PawelZietek/Hexapod-with-Raspberry-and-Maestro/pics, diagrams, videos/0J9911.600x480.jpg

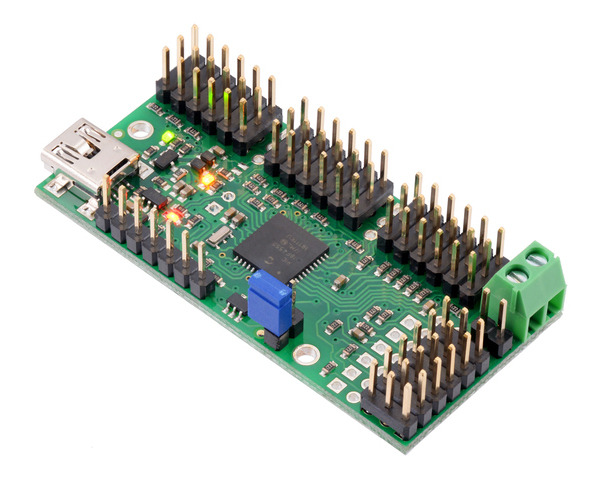
pics, diagrams, videos/0J9911.600x480.jpg
