PawelZietek/Hexapod-with-Raspberry-and-Maestro/pics, diagrams, videos/arm rotating.jpg

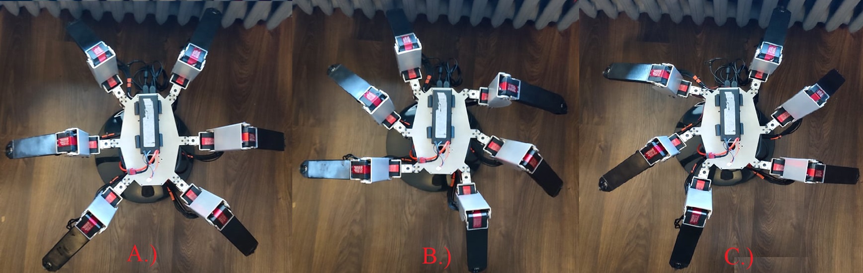
pics, diagrams, videos/arm rotating.jpg
