PawelZietek/Hexapod-with-Raspberry-and-Maestro/pics, diagrams, videos/femurupand down.jpg

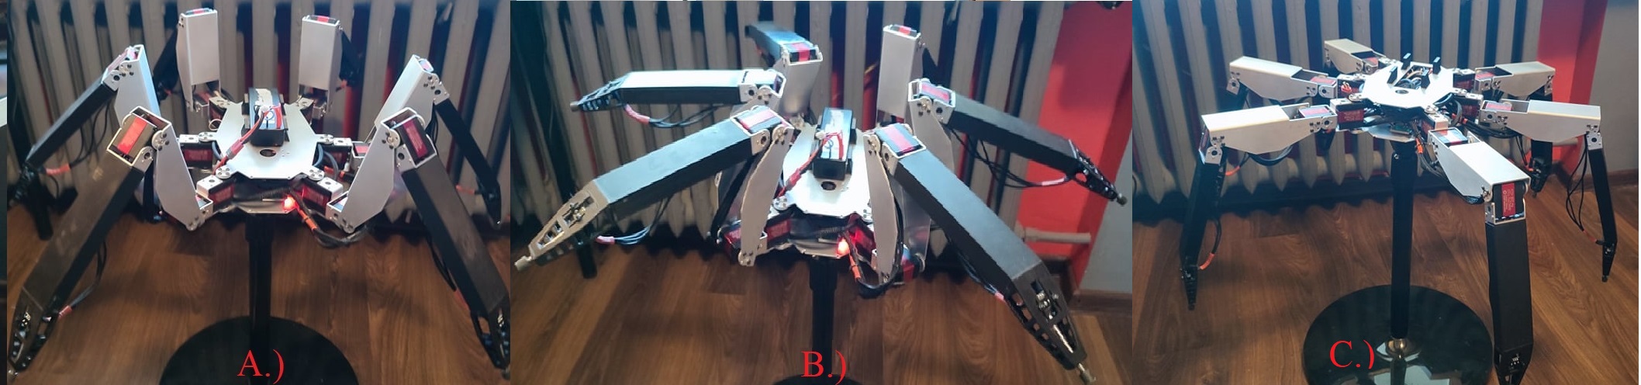
pics, diagrams, videos/femurupand down.jpg
