PawelZietek/Hexapod-with-Raspberry-and-Maestro/pics, diagrams, videos/foot.png

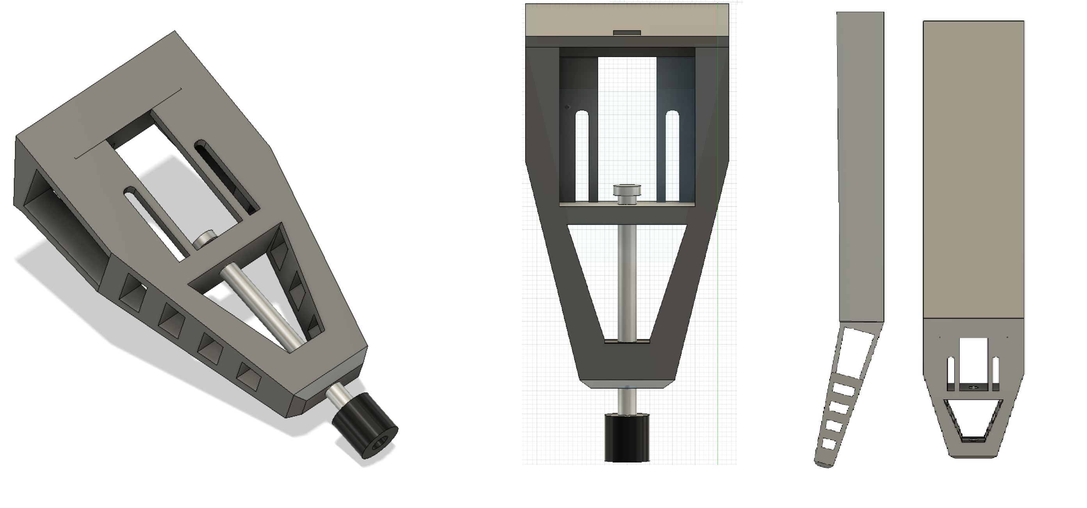
pics, diagrams, videos/foot.png
