PawelZietek/Hexapod-with-Raspberry-and-Maestro/pics, diagrams, videos/forwardbacwardsequence.PNG

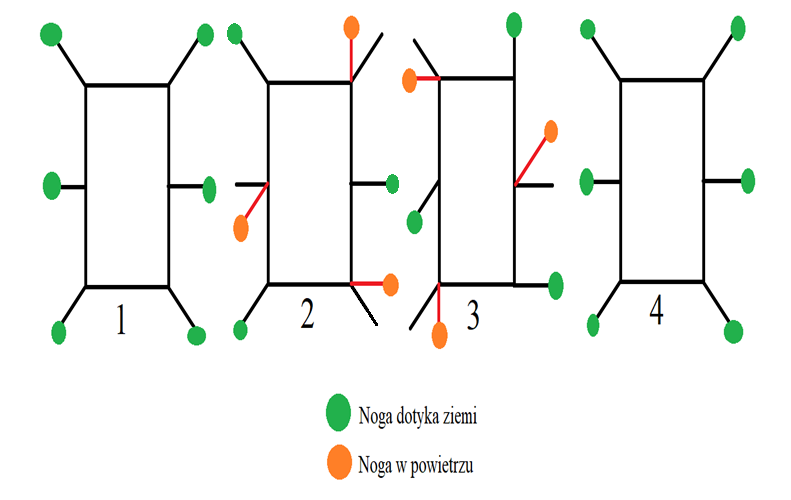
pics, diagrams, videos/forwardbacwardsequence.PNG
