PawelZietek/Hexapod-with-Raspberry-and-Maestro/pics, diagrams, videos/gpio connection.png

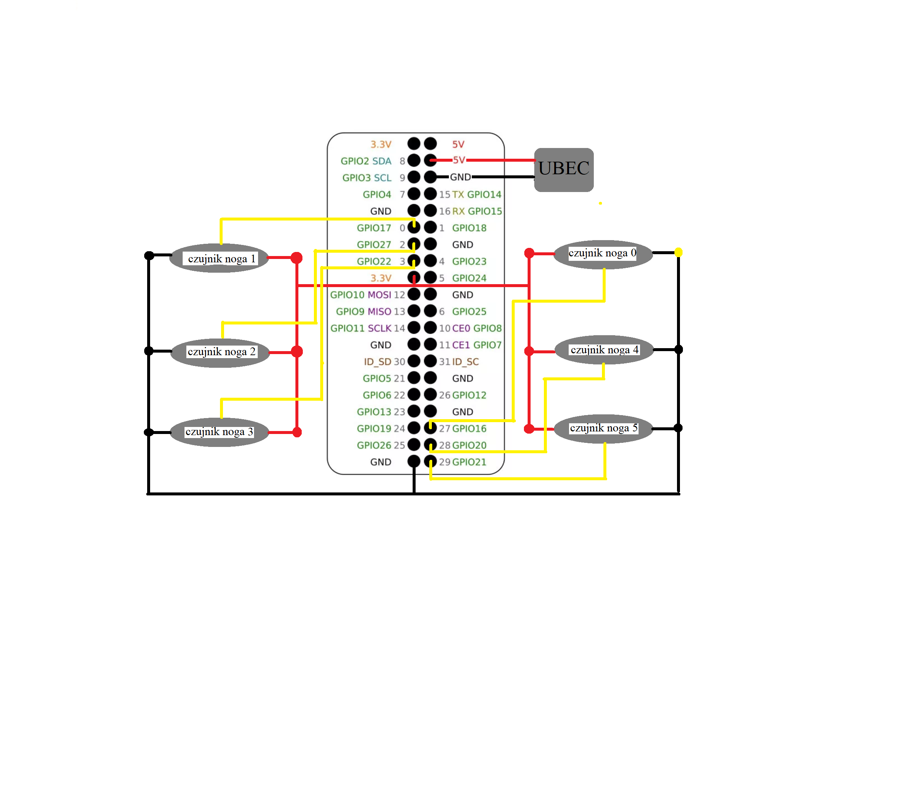
pics, diagrams, videos/gpio connection.png
