PawelZietek/Hexapod-with-Raspberry-and-Maestro/pics, diagrams, videos/hexapod_drawings 1.PNG

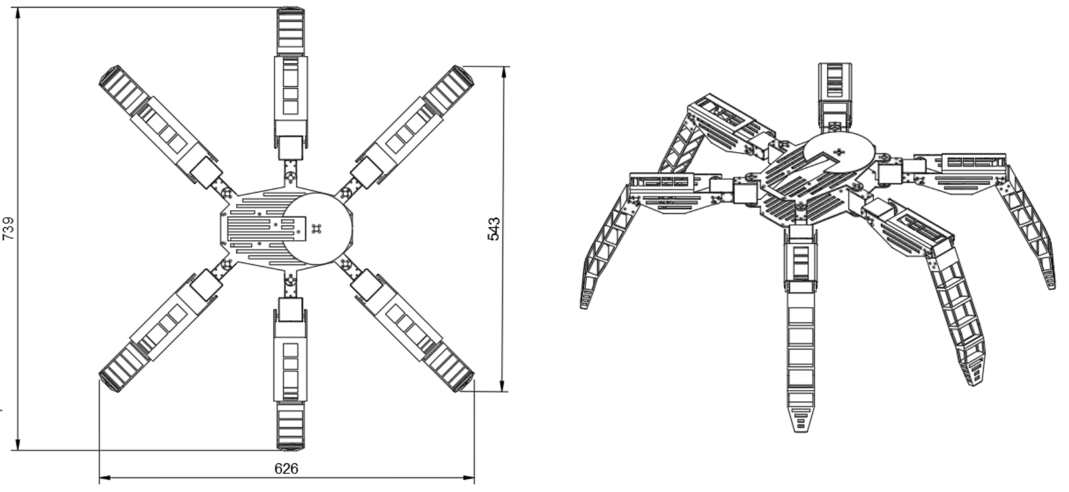
pics, diagrams, videos/hexapod_drawings 1.PNG
