PawelZietek/Hexapod-with-Raspberry-and-Maestro/pics, diagrams, videos/hexapod_drawings 3.PNG

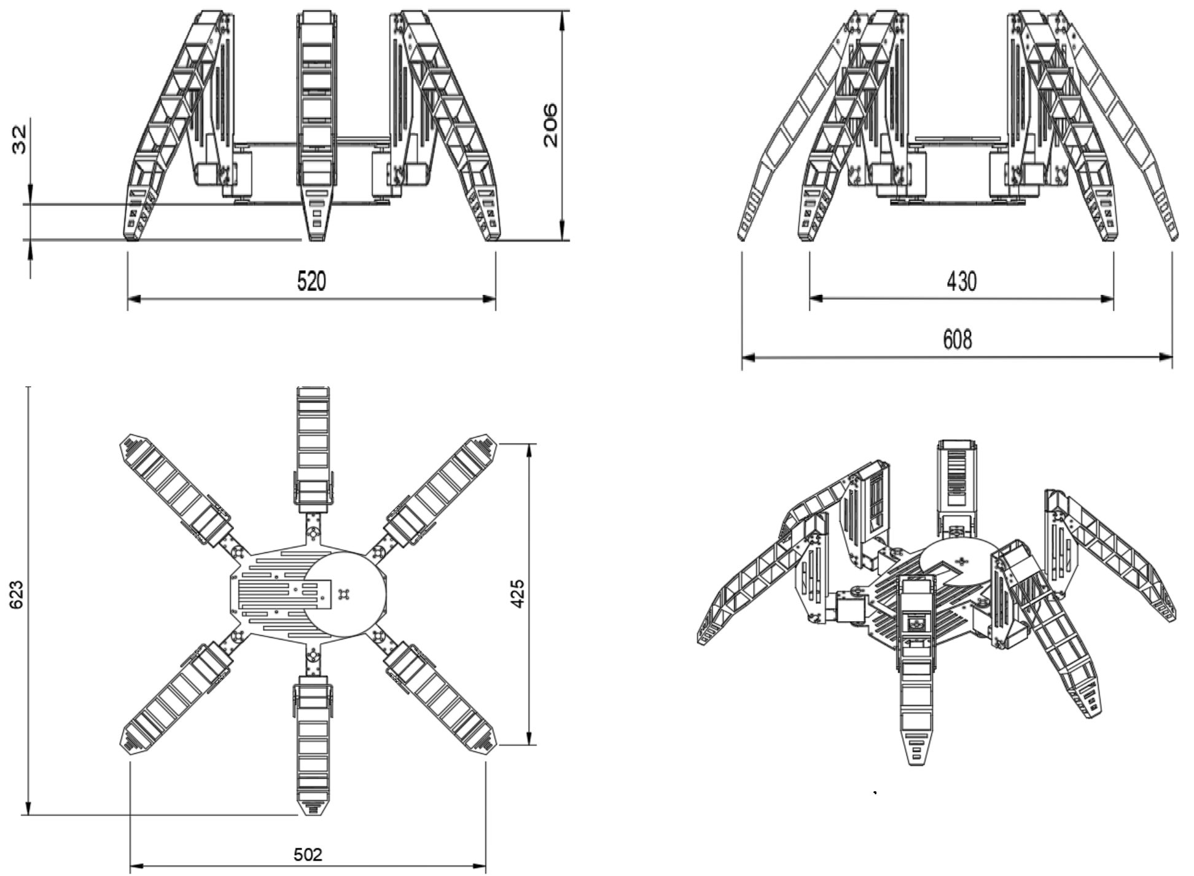
pics, diagrams, videos/hexapod_drawings 3.PNG
