PawelZietek/Hexapod-with-Raspberry-and-Maestro/pics, diagrams, videos/hexapod_project_fusion 1.PNG

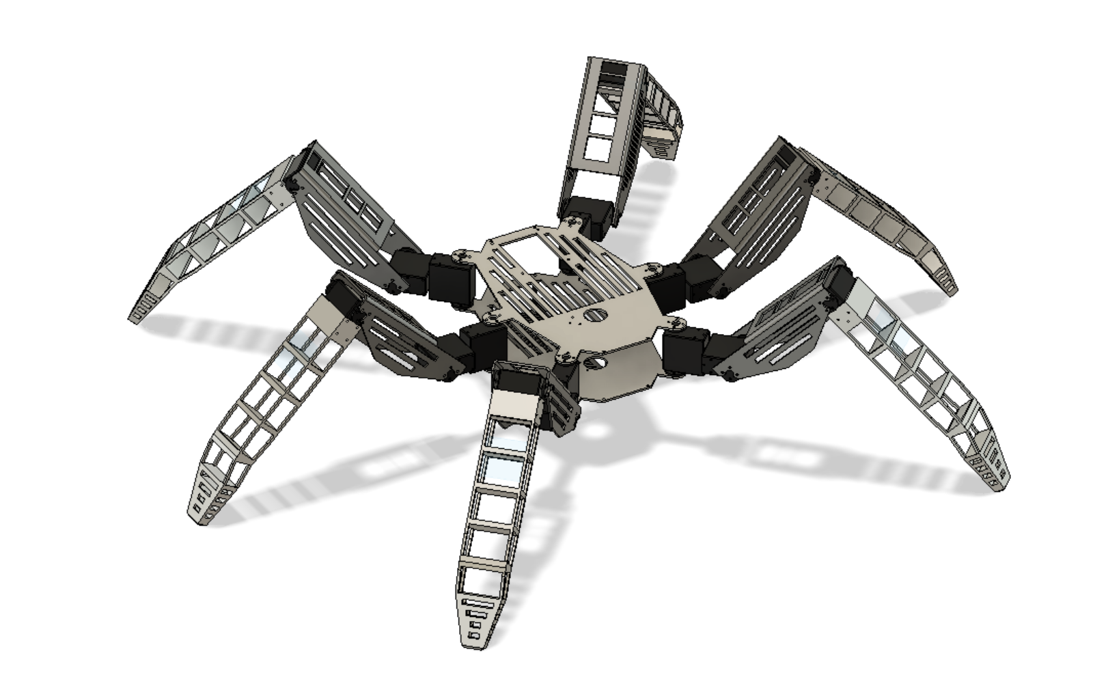
pics, diagrams, videos/hexapod_project_fusion 1.PNG
