PawelZietek/Hexapod-with-Raspberry-and-Maestro/pics, diagrams, videos/hexapod_project_fusion 3.PNG

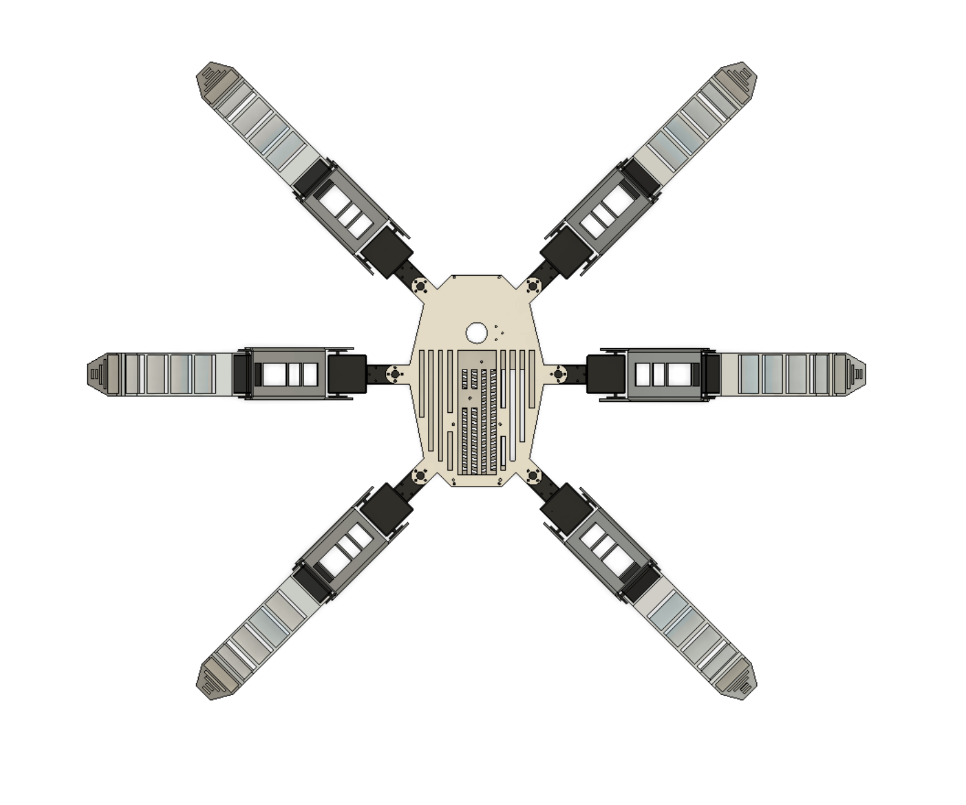
pics, diagrams, videos/hexapod_project_fusion 3.PNG
