PawelZietek/Hexapod-with-Raspberry-and-Maestro/pics, diagrams, videos/hexapod_project_fusion 4.PNG

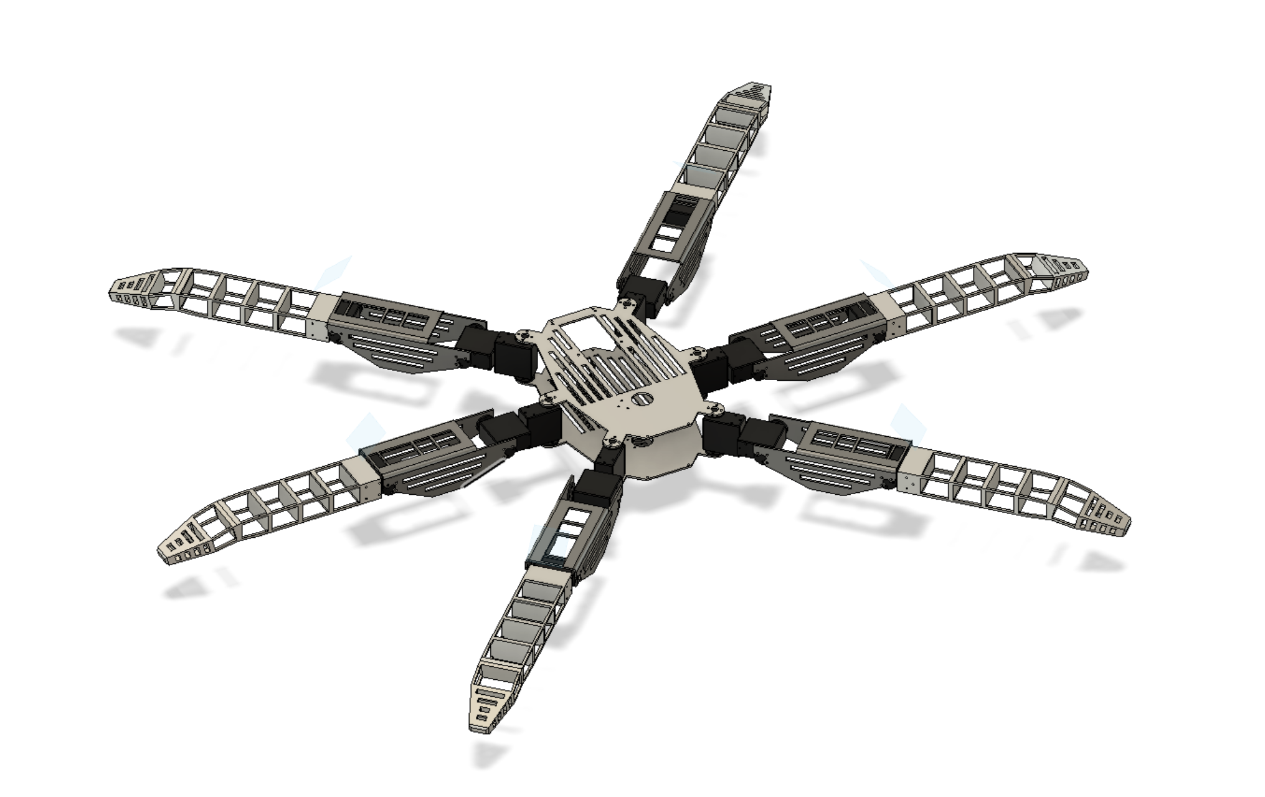
pics, diagrams, videos/hexapod_project_fusion 4.PNG
