PawelZietek/Hexapod-with-Raspberry-and-Maestro/pics, diagrams, videos/hexapod_project_fusion 6.png

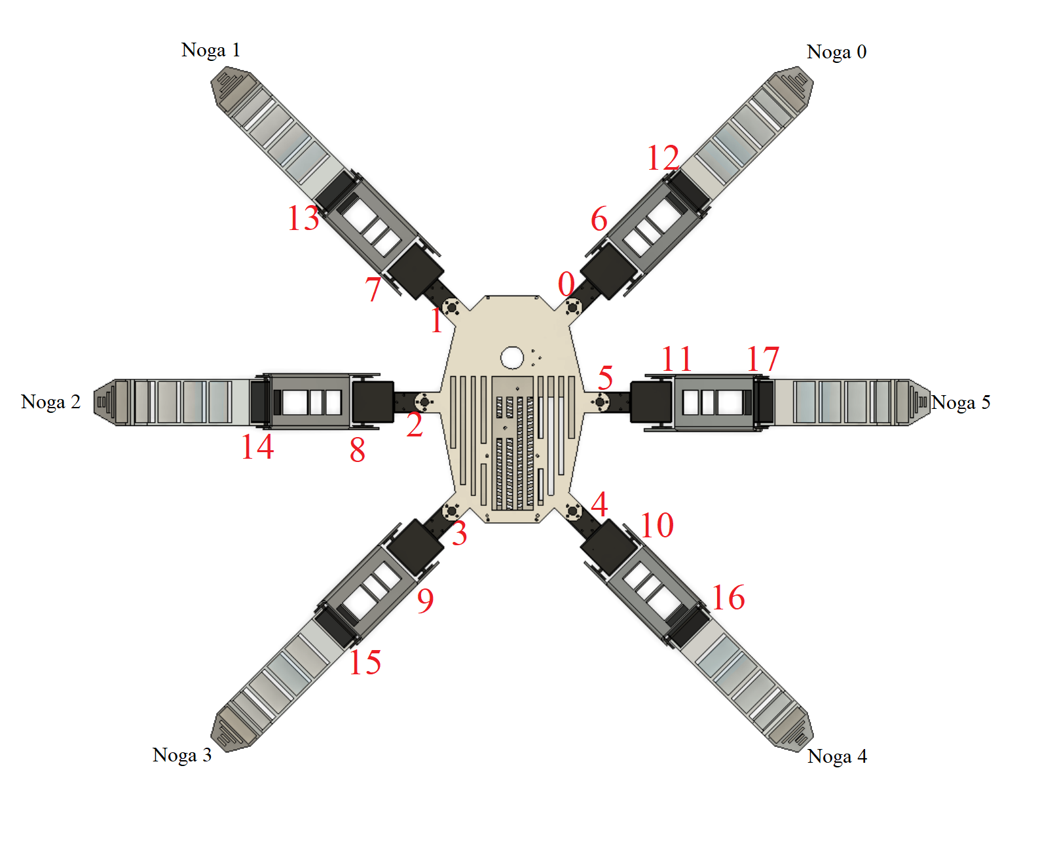
pics, diagrams, videos/hexapod_project_fusion 6.png
