PawelZietek/Hexapod-with-Raspberry-and-Maestro/pics, diagrams, videos/leg.png

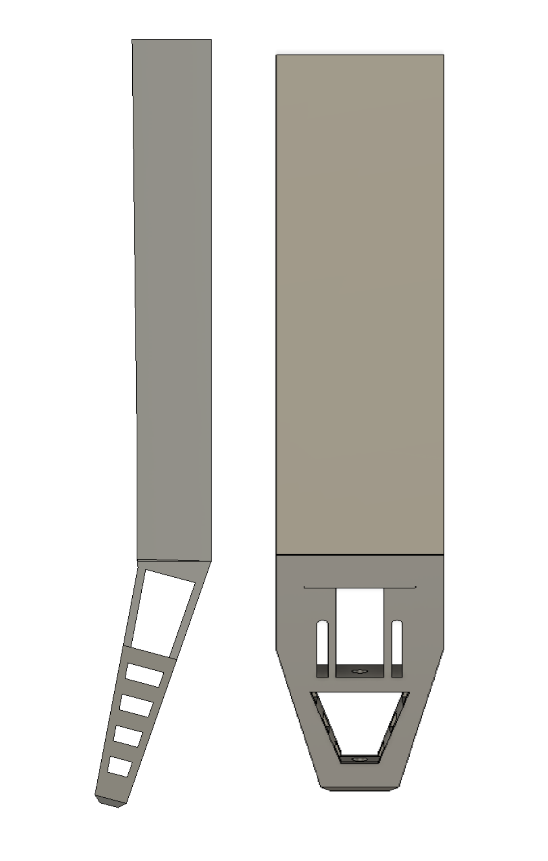
pics, diagrams, videos/leg.png
