PawelZietek/Hexapod-with-Raspberry-and-Maestro/pics, diagrams, videos/rds3225.webp

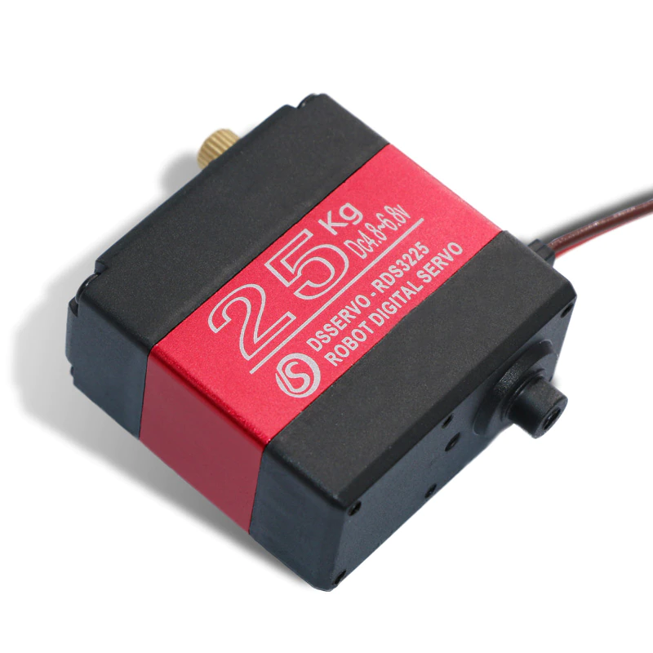
pics, diagrams, videos/rds3225.webp
