PawelZietek/Hexapod-with-Raspberry-and-Maestro/pics, diagrams, videos/seqForwardBackward.png

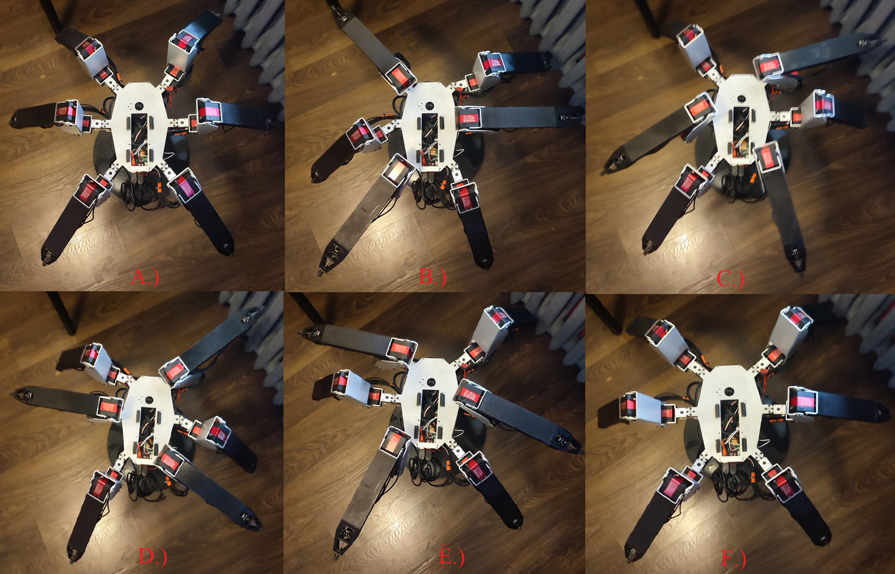
pics, diagrams, videos/seqForwardBackward.png
