PawelZietek/Hexapod-with-Raspberry-and-Maestro/pics, diagrams, videos/sequence of rotating.png

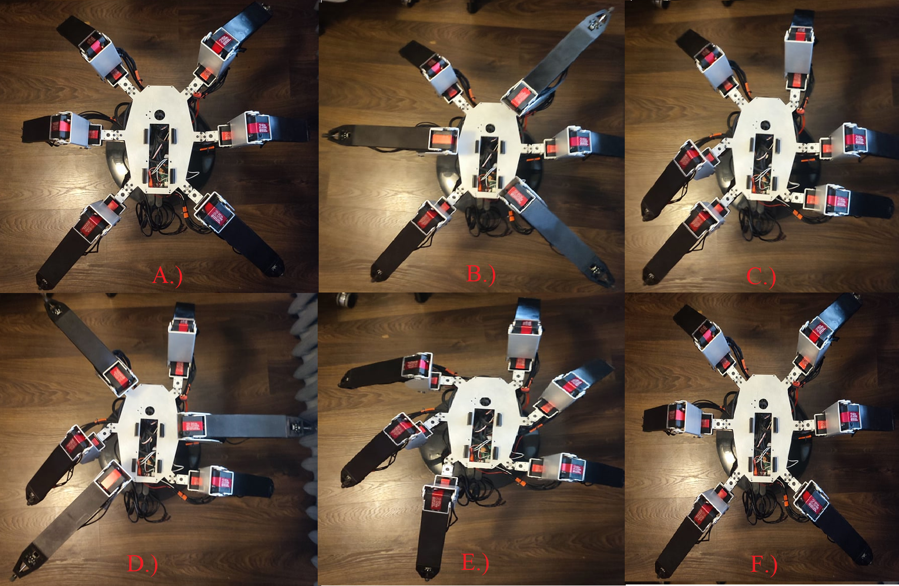
pics, diagrams, videos/sequence of rotating.png
