PawelZietek/Hexapod-with-Raspberry-and-Maestro/pics, diagrams, videos/sequence rotatin.png

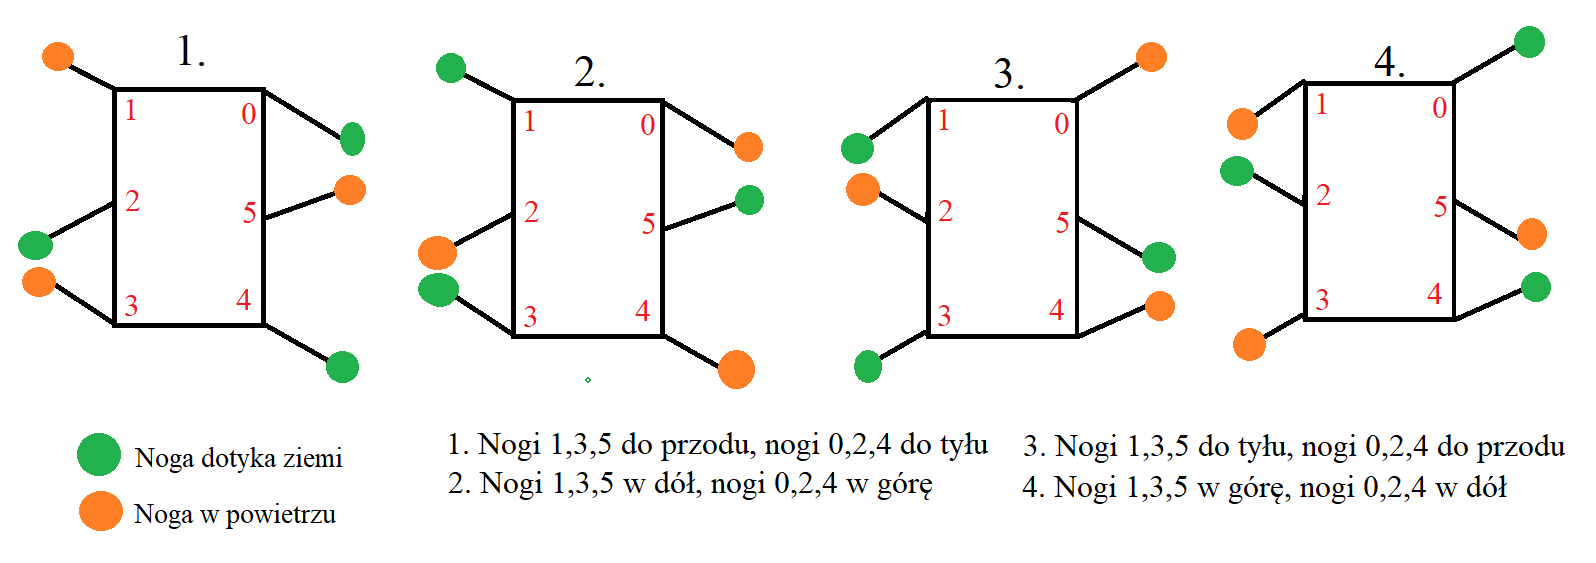
pics, diagrams, videos/sequence rotatin.png
