PawelZietek/Hexapod-with-Raspberry-and-Maestro/pics, diagrams, videos/tibia up and down.png

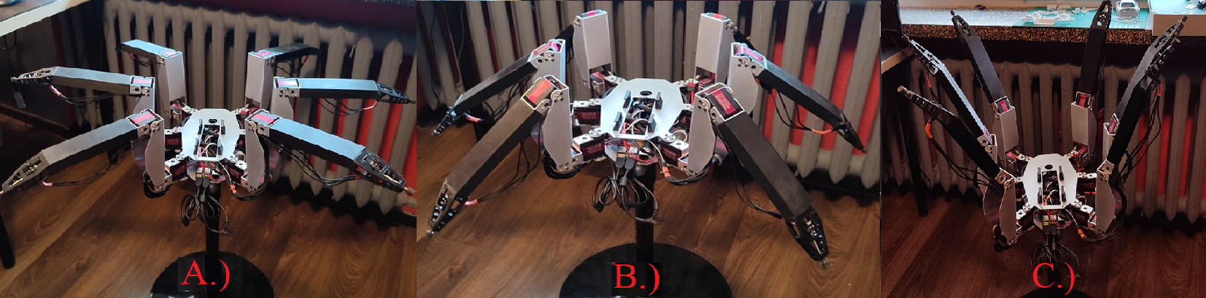
pics, diagrams, videos/tibia up and down.png
