PawelZietek/Hexapod-with-Raspberry-and-Maestro/hexapod_main/threads.py

import threading
  
def print_cube(num):
    """
    function to print cube of given num
    """
    print("Cube: {}".format(num * num * num))
  

t1 = threading.Thread(target=print_cube, args=(5,))
t2 = threading.Thread(target=print_cube, args=(10,))
  
    # starting thread 1
t1.start()
    # starting thread 2
t2.start()
  
    # wait until thread 1 is completely executed
t1.join()
    # wait until thread 2 is completely executed
t2.join()
  
    # both threads completely executed
print("Done!")
